Atharv-Shukla-987/Talking-Mirror/talking_mirror/talking_mirror.kicad_pcb

## KiCad design hardware/control_board/control_board.kicad_pcb

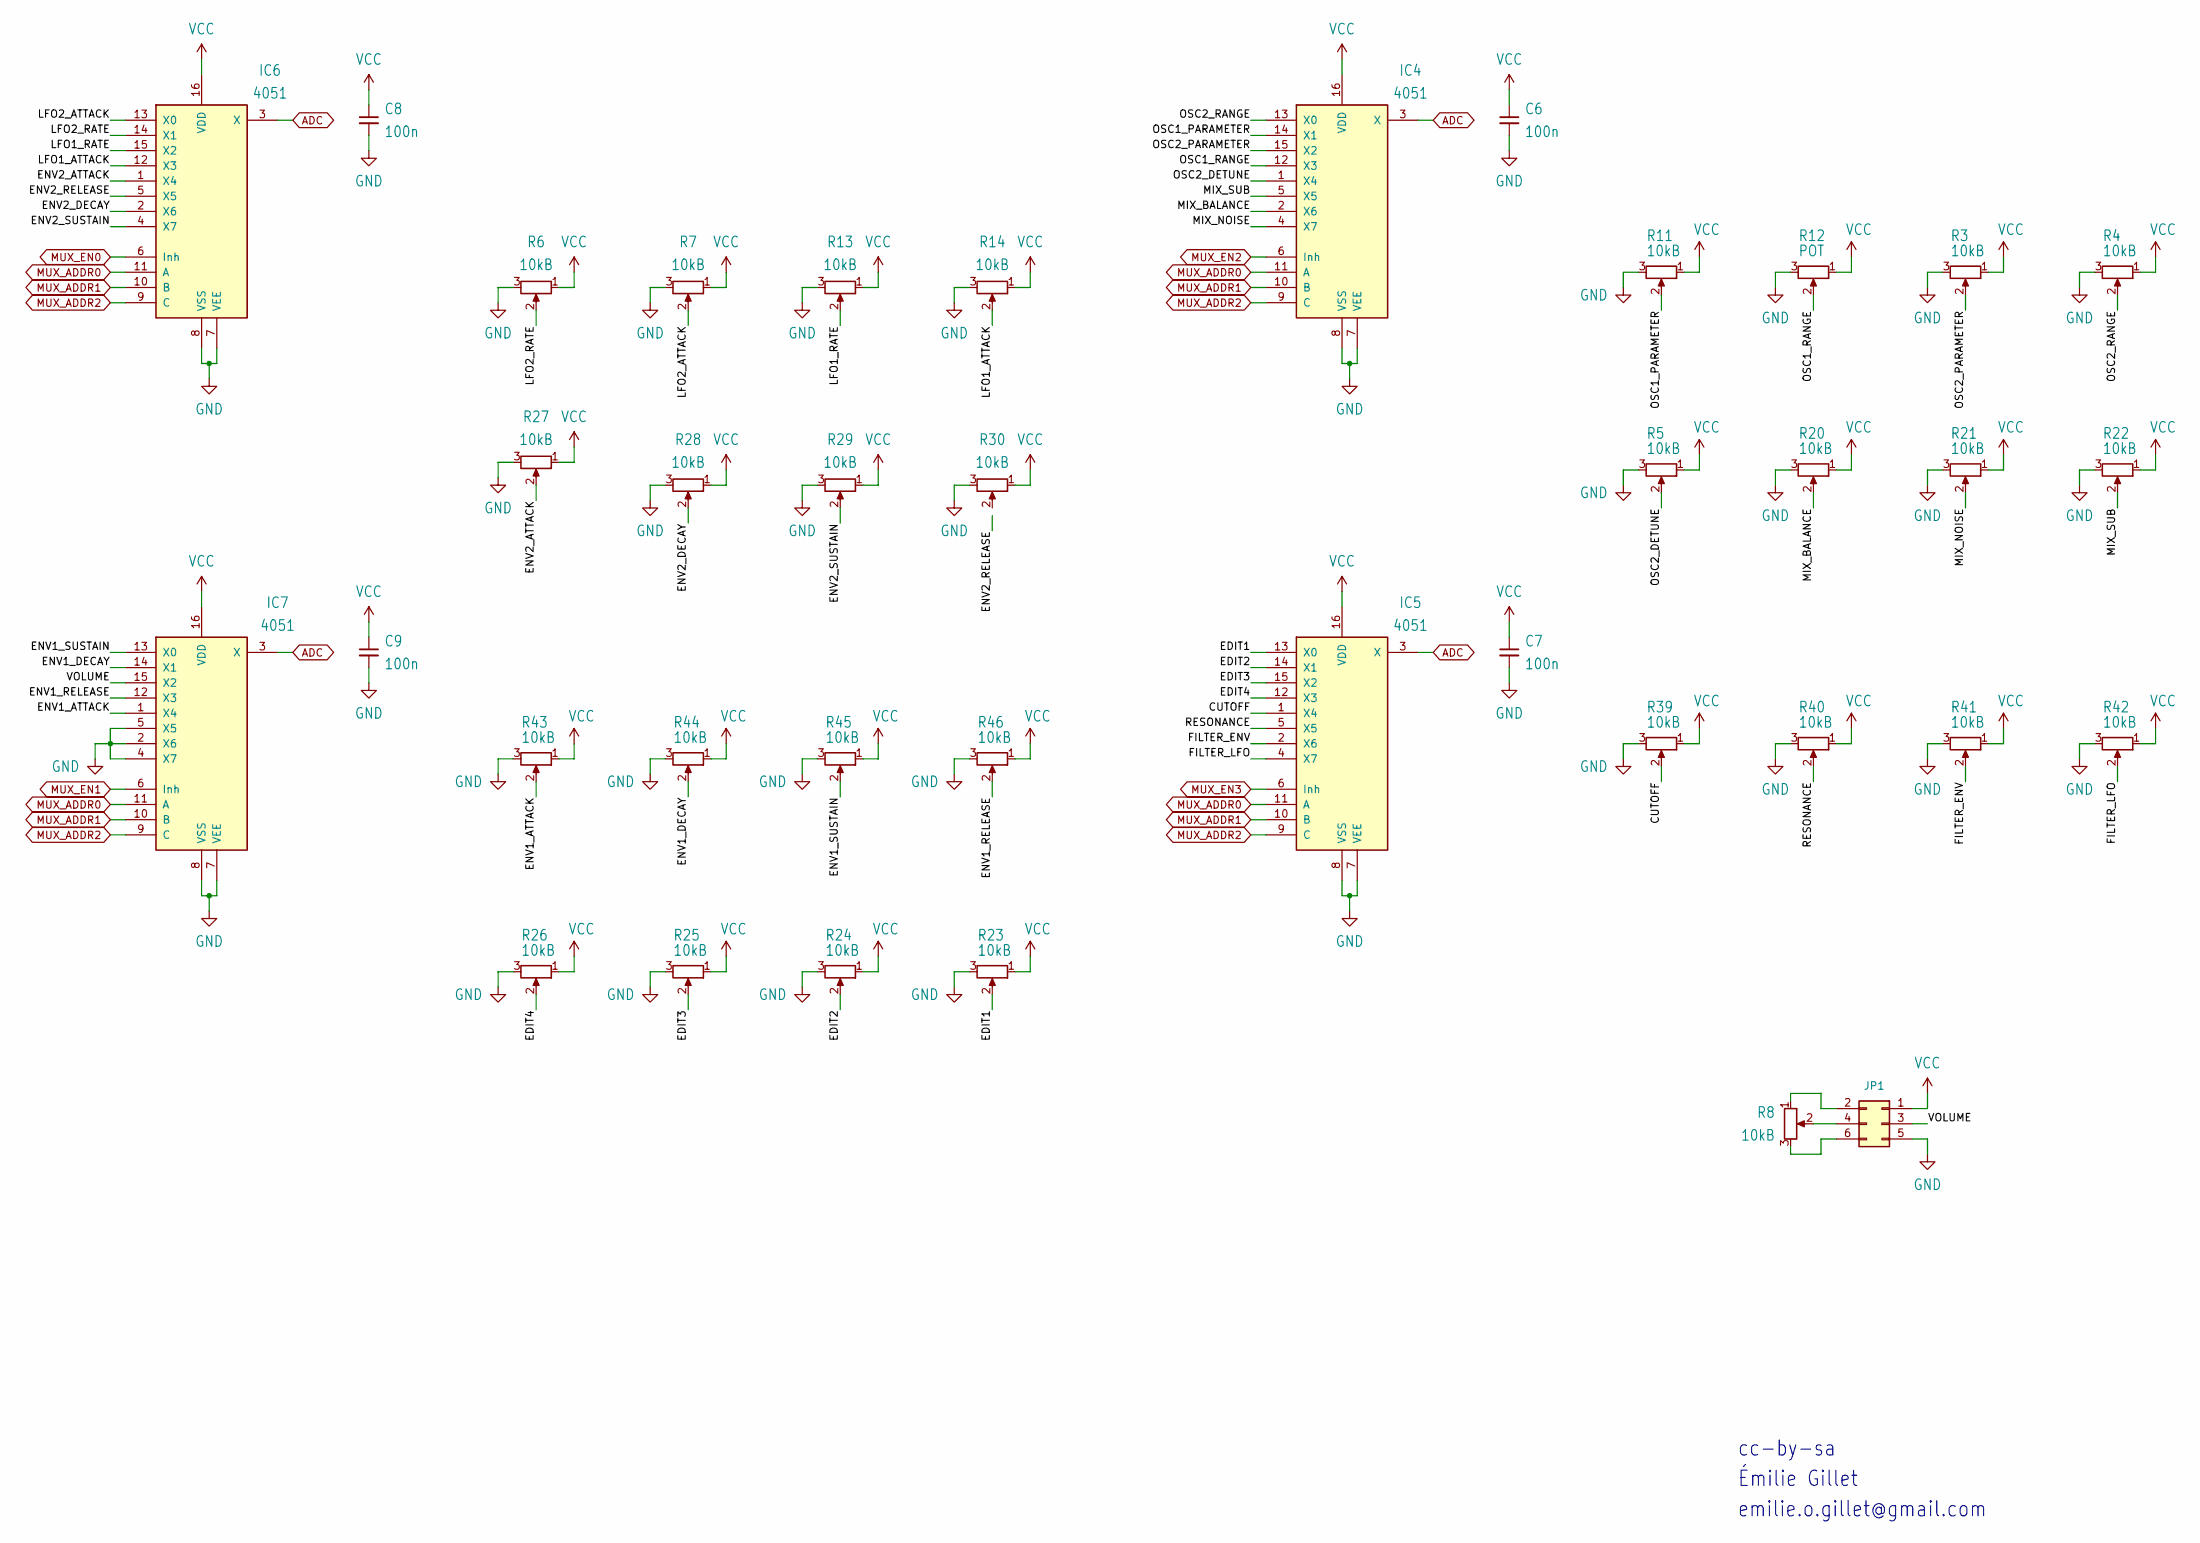
[picture p6: schematic pots.kicad_sch]

Parts:
C6, C7, C8, C9: 100n; C025-024X044
IC4, IC5, IC6, IC7: 4051; DIP-16_W7.62mm_Socket_LongPads
JP1: Conn_02x03_Odd_Even; PinHeader_2x03_P2.54mm_Vertical
R3, R4, R5, R6, R7, R8, R11, R13, R14, R20, R21, R22, R23, R24, R25, R26, R27, R28, R29, R30, R39, R40, R41, R42, R43, R44, R45, R46: 10kB; ALPS_POT_VERTICAL
R12: POT; ALPS_POT_VERTICAL

Connections:
/pots/CUTOFF: IC5.1 (X4), R39.2
/pots/EDIT1: IC5.13 (X0), R23.2
/pots/EDIT2: IC5.14 (X1), R24.2
/pots/EDIT3: IC5.15 (X2), R25.2
/pots/EDIT4: IC5.12 (X3), R26.2
/pots/ENV1_ATTACK: IC7.1 (X4), R43.2
/pots/ENV1_DECAY: IC7.14 (X1), R44.2
/pots/ENV1_RELEASE: IC7.12 (X3), R46.2
/pots/ENV1_SUSTAIN: IC7.13 (X0), R45.2
/pots/ENV2_ATTACK: IC6.1 (X4), R27.2
/pots/ENV2_DECAY: IC6.2 (X6), R28.2
/pots/ENV2_RELEASE: IC6.5 (X5)
/pots/ENV2_SUSTAIN: IC6.4 (X7), R29.2
/pots/FILTER_ENV: IC5.2 (X6), R41.2
/pots/FILTER_LFO: IC5.4 (X7), R42.2
/pots/LFO1_ATTACK: IC6.12 (X3), R14.2
/pots/LFO1_RATE: IC6.15 (X2), R13.2
/pots/LFO2_ATTACK: IC6.13 (X0), R7.2
/pots/LFO2_RATE: IC6.14 (X1), R6.2
/pots/MIX_BALANCE: IC4.2 (X6), R20.2
/pots/MIX_NOISE: IC4.4 (X7), R21.2
/pots/MIX_SUB: IC4.5 (X5), R22.2
/pots/OSC1_PARAMETER: IC4.14 (X1), R11.2
/pots/OSC1_RANGE: IC4.12 (X3), R12.2
/pots/OSC2_DETUNE: IC4.1 (X4), R5.2
/pots/OSC2_PARAMETER: IC4.15 (X2), R3.2
/pots/OSC2_RANGE: IC4.13 (X0), R4.2
/pots/RESONANCE: IC5.5 (X5), R40.2
/pots/VOLUME: IC7.15 (X2), JP1.3
ADC: IC4.3 (X), IC5.3 (X), IC6.3 (X), IC7.3 (X); also elsewhere on the board
GND: C6.2, C7.2, C8.2, C9.2, IC4.7 (VEE), IC4.8 (VSS), IC5.7 (VEE), IC5.8 (VSS), IC6.7 (VEE), IC6.8 (VSS), IC7.2 (X6), IC7.4 (X7), IC7.5 (X5), IC7.7 (VEE), IC7.8 (VSS), JP1.5, R3.3, R4.3, R5.3, R6.3, R7.3, R11.3, R12.3, R13.3, R14.3, R20.3, R21.3, R22.3, R23.3, R24.3, R25.3, R26.3, R27.3, R28.3, R29.3, R30.3, R39.3, R40.3, R41.3, R42.3, R43.3, R44.3, R45.3, R46.3; also elsewhere on the board
MUX_ADDR0: IC4.11 (A), IC5.11 (A), IC6.11 (A), IC7.11 (A); also elsewhere on the board
MUX_ADDR1: IC4.10 (B), IC5.10 (B), IC6.10 (B), IC7.10 (B); also elsewhere on the board
MUX_ADDR2: IC4.9 (C), IC5.9 (C), IC6.9 (C), IC7.9 (C); also elsewhere on the board
MUX_EN0: IC6.6 (Inh); also elsewhere on the board
MUX_EN1: IC7.6 (Inh); also elsewhere on the board
MUX_EN2: IC4.6 (Inh); also elsewhere on the board
MUX_EN3: IC5.6 (Inh); also elsewhere on the board
unnamed: JP1.2, R8.1
unnamed: JP1.4, R8.2
unnamed: JP1.6, R8.3
VCC: C6.1, C7.1, C8.1, C9.1, IC4.16 (VDD), IC5.16 (VDD), IC6.16 (VDD), IC7.16 (VDD), JP1.1, R3.1, R4.1, R5.1, R6.1, R7.1, R11.1, R12.1, R13.1, R14.1, R20.1, R21.1, R22.1, R23.1, R24.1, R25.1, R26.1, R27.1, R28.1, R29.1, R30.1, R39.1, R40.1, R41.1, R42.1, R43.1, R44.1, R45.1, R46.1; also elsewhere on the board

Notes on the sheet:
emilie.o.gillet@gmail.com
cc-by-sa
Émilie Gillet

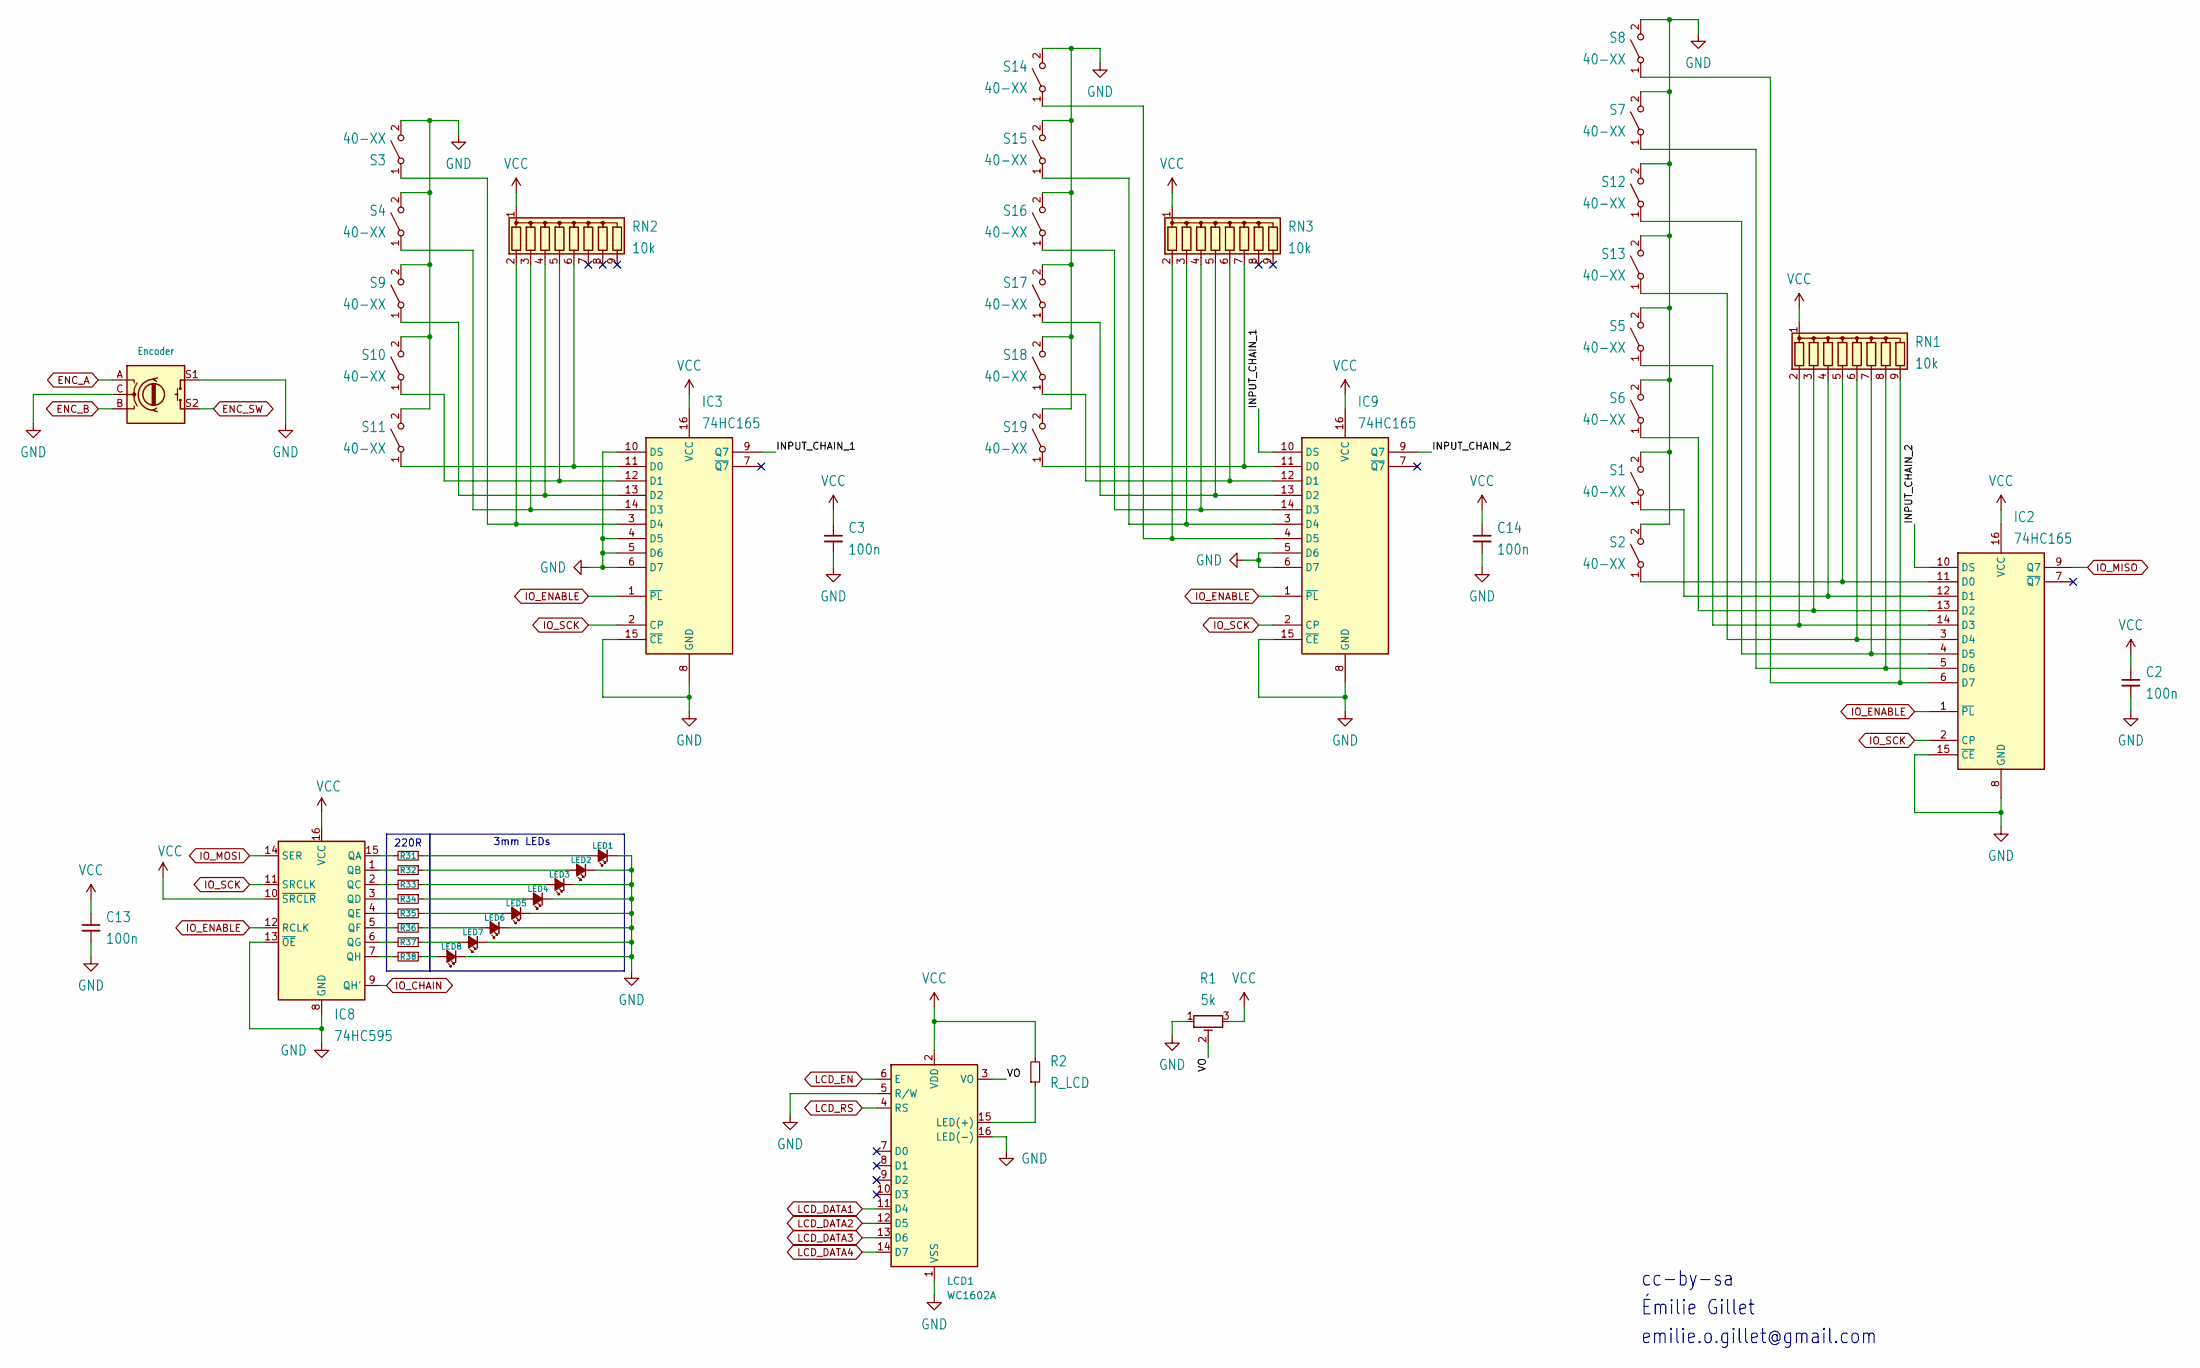
[picture p7: schematic buttons.kicad_sch]

Parts:
C2, C3, C13, C14: 100n; C025-024X044
IC2, IC3, IC9: 74HC165; DIP-16_W7.62mm_Socket_LongPads
IC8: 74HC595; DIP-16_W7.62mm_Socket_LongPads
LCD1: WC1602A
LED1, LED2, LED3, LED4, LED5, LED6, LED7, LED8: LED3MM; LED_D3.0mm
R1: 5k; Potentiometer_Bourns_3296W_Vertical
R2: R_LCD; R_Axial_DIN0204_L3.6mm_D1.6mm_P7.62mm_Horizontal
R31, R32, R33, R34, R35, R36, R37, R38: 220; R_Axial_DIN0204_L3.6mm_D1.6mm_P7.62mm_Horizontal
RN1, RN2, RN3: 10k; R_Array_SIP9
S1, S2, S3, S4, S5, S6, S7, S8, S9, S10, S11, S12, S13, S14, S15, S16, S17, S18, S19: 40-XX; B3F-40XX
SW1: Encoder; ALPS_EC12E_SW

Connections:
/buttons/INPUT_CHAIN_1: IC3.9 (Q7), IC9.10 (DS)
/buttons/INPUT_CHAIN_2: IC2.10 (DS), IC9.9 (Q7)
/buttons/VO: LCD1.3 (VO), R1.2
ENC_A: SW1.A; also elsewhere on the board
ENC_B: SW1.B; also elsewhere on the board
ENC_SW: SW1.S2; also elsewhere on the board
GND: C2.2, C3.2, C13.2, C14.2, IC2.8 (GND), IC2.15 (~CE), IC3.4 (D5), IC3.5 (D6), IC3.6 (D7), IC3.8 (GND), IC3.10 (DS), IC3.15 (~CE), IC8.8 (GND), IC8.13 (~OE), IC9.5 (D6), IC9.6 (D7), IC9.8 (GND), IC9.15 (~CE), LCD1.1 (VSS), LCD1.5 (R/W), LCD1.16 (LED(-)), LED1.1 (K), LED2.1 (K), LED3.1 (K), LED4.1 (K), LED5.1 (K), LED6.1 (K), LED7.1 (K), LED8.1 (K), R1.1, S1.2 (B), S2.2 (B), S3.2 (B), S4.2 (B), S5.2 (B), S6.2 (B), S7.2 (B), S8.2 (B), S9.2 (B), S10.2 (B), S11.2 (B), S12.2 (B), S13.2 (B), S14.2 (B), S15.2 (B), S16.2 (B), S17.2 (B), S18.2 (B), S19.2 (B), SW1.C, SW1.S1; also elsewhere on the board
IO_CHAIN: IC8.9 (QH'); also elsewhere on the board
IO_ENABLE: IC2.1 (~PL), IC3.1 (~PL), IC8.12 (RCLK), IC9.1 (~PL); also elsewhere on the board
IO_MISO: IC2.9 (Q7); also elsewhere on the board
IO_MOSI: IC8.14 (SER); also elsewhere on the board
IO_SCK: IC2.2 (CP), IC3.2 (CP), IC8.11 (SRCLK), IC9.2 (CP); also elsewhere on the board
LCD_DATA1: LCD1.11 (D4); also elsewhere on the board
LCD_DATA2: LCD1.12 (D5); also elsewhere on the board
LCD_DATA3: LCD1.13 (D6); also elsewhere on the board
LCD_DATA4: LCD1.14 (D7); also elsewhere on the board
LCD_EN: LCD1.6 (E); also elsewhere on the board
LCD_RS: LCD1.4 (RS); also elsewhere on the board
unnamed: IC2.11 (D0), RN1.5 (R4), S2.1 (A)
unnamed: IC2.12 (D1), RN1.4 (R3), S1.1 (A)
unnamed: IC2.13 (D2), RN1.3 (R2), S6.1 (A)
unnamed: IC2.14 (D3), RN1.2 (R1), S5.1 (A)
unnamed: IC2.3 (D4), RN1.6 (R5), S13.1 (A)
unnamed: IC2.4 (D5), RN1.7 (R6), S12.1 (A)
unnamed: IC2.5 (D6), RN1.8 (R7), S7.1 (A)
unnamed: IC2.6 (D7), RN1.9 (R8), S8.1 (A)
unnamed: IC3.11 (D0), RN2.6 (R5), S11.1 (A)
unnamed: IC3.12 (D1), RN2.5 (R4), S10.1 (A)
unnamed: IC3.13 (D2), RN2.4 (R3), S9.1 (A)
unnamed: IC3.14 (D3), RN2.3 (R2), S4.1 (A)
unnamed: IC3.3 (D4), RN2.2 (R1), S3.1 (A)
unnamed: IC8.15 (QA), R31.2
unnamed: IC8.1 (QB), R32.2
unnamed: IC8.2 (QC), R33.2
unnamed: IC8.3 (QD), R34.2
unnamed: IC8.4 (QE), R35.2
unnamed: IC8.5 (QF), R36.2
unnamed: IC8.6 (QG), R37.2
unnamed: IC8.7 (QH), R38.2
unnamed: IC9.11 (D0), RN3.7 (R6), S19.1 (A)
unnamed: IC9.12 (D1), RN3.6 (R5), S18.1 (A)
unnamed: IC9.13 (D2), RN3.5 (R4), S17.1 (A)
unnamed: IC9.14 (D3), RN3.4 (R3), S16.1 (A)
unnamed: IC9.3 (D4), RN3.3 (R2), S15.1 (A)
unnamed: IC9.4 (D5), RN3.2 (R1), S14.1 (A)
unnamed: LCD1.15 (LED(+)), R2.1
unnamed: LED1.2 (A), R31.1
unnamed: LED2.2 (A), R32.1
unnamed: LED3.2 (A), R33.1
unnamed: LED4.2 (A), R34.1
unnamed: LED5.2 (A), R35.1
unnamed: LED6.2 (A), R36.1
unnamed: LED7.2 (A), R37.1
unnamed: LED8.2 (A), R38.1
VCC: C2.1, C3.1, C13.1, C14.1, IC2.16 (VCC), IC3.16 (VCC), IC8.10 (~SRCLR), IC8.16 (VCC), IC9.16 (VCC), LCD1.2 (VDD), R1.3, R2.2, RN1.1 (common), RN2.1 (common), RN3.1 (common); also elsewhere on the board

Notes on the sheet:
220R
3mm LEDs
emilie.o.gillet@gmail.com
Émilie Gillet
cc-by-sa

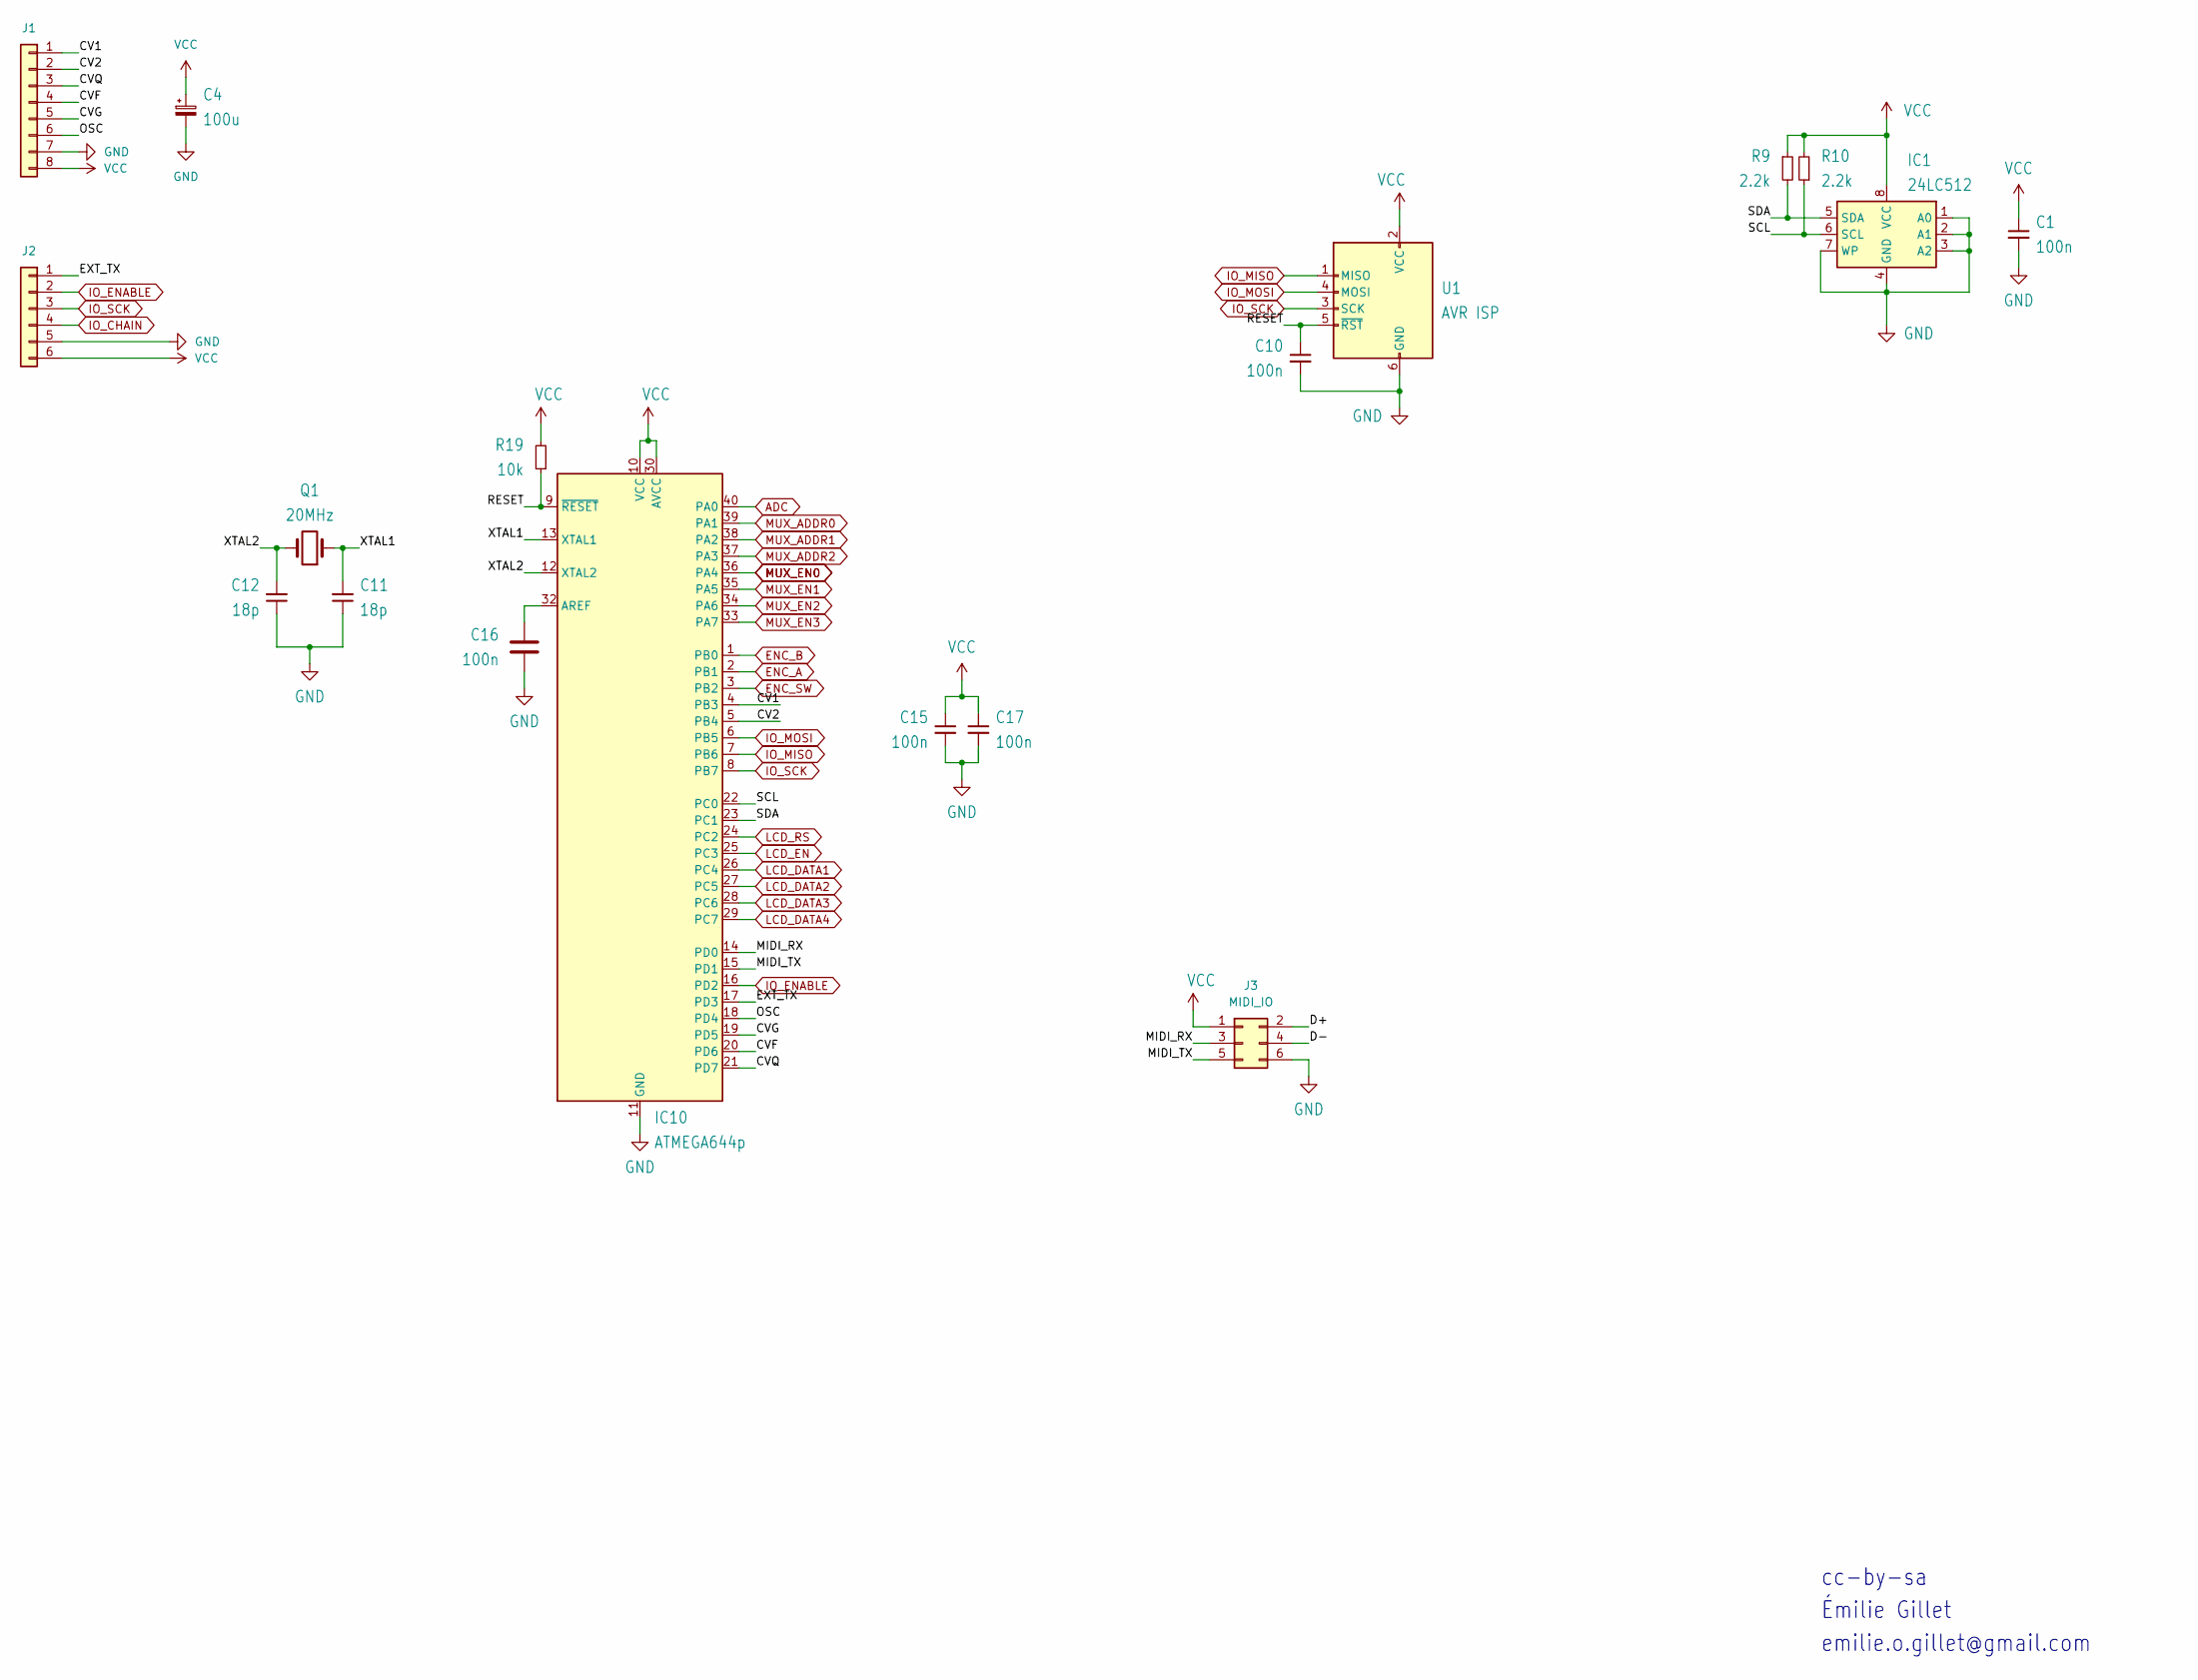
[picture p8: schematic mcu.kicad_sch]

Parts:
C1, C10, C15, C16, C17: 100n; C025-024X044
C4: 100u; CP_Radial_D6.3mm_P2.50mm
C11, C12: 18p; C025-024X044
IC1: 24LC512; DIP-8_W7.62mm_Socket_LongPads
IC10: ATMEGA644p; DIP-40_W15.24mm_Socket_LongPads
J1: Conn_01x08; PinHeader_1x08_P2.54mm_Vertical
J2: Conn_01x06; PinHeader_1x06_P2.54mm_Vertical
J3: MIDI_IO; PinHeader_2x03_P2.54mm_Vertical
Q1: 20MHz; HC49U-V
R9, R10: 2.2k; R_Axial_DIN0204_L3.6mm_D1.6mm_P7.62mm_Horizontal
R19: 10k; 0204_7
U1: AVR ISP; PinHeader_2x03_P2.54mm_Vertical

Connections:
/mcu/CV1: IC10.4 (PB3), J1.1
/mcu/CV2: IC10.5 (PB4), J1.2
/mcu/CVF: IC10.20 (PD6), J1.4
/mcu/CVG: IC10.19 (PD5), J1.5
/mcu/CVQ: IC10.21 (PD7), J1.3
/mcu/D+: J3.2
/mcu/D-: J3.4
/mcu/EXT_TX: IC10.17 (PD3), J2.1
/mcu/MIDI_RX: IC10.14 (PD0), J3.3
/mcu/MIDI_TX: IC10.15 (PD1), J3.5
/mcu/OSC: IC10.18 (PD4), J1.6
/mcu/RESET: C10.1, IC10.9 (~RESET), R19.1, U1.5 (~RST)
/mcu/SCL: IC1.6 (SCL), IC10.22 (PC0), R10.1
/mcu/SDA: IC1.5 (SDA), IC10.23 (PC1), R9.2
/mcu/XTAL1: C11.2, IC10.13 (XTAL1), Q1.1
/mcu/XTAL2: C12.2, IC10.12 (XTAL2), Q1.2
ADC: IC10.40 (PA0); also elsewhere on the board
ENC_A: IC10.2 (PB1); also elsewhere on the board
ENC_B: IC10.1 (PB0); also elsewhere on the board
ENC_SW: IC10.3 (PB2); also elsewhere on the board
GND: C1.2, C4.2, C10.2, C11.1, C12.1, C15.2, C16.2, C17.2, IC1.1 (A0), IC1.2 (A1), IC1.3 (A2), IC1.4 (GND), IC1.7 (WP), IC10.11 (GND), IC10.31 (GND), J1.7, J2.5, J3.6, U1.6 (GND); also elsewhere on the board
IO_CHAIN: J2.4; also elsewhere on the board
IO_ENABLE: IC10.16 (PD2), J2.2; also elsewhere on the board
IO_MISO: IC10.7 (PB6), U1.1 (MISO); also elsewhere on the board
IO_MOSI: IC10.6 (PB5), U1.4 (MOSI); also elsewhere on the board
IO_SCK: IC10.8 (PB7), J2.3, U1.3 (SCK); also elsewhere on the board
LCD_DATA1: IC10.26 (PC4); also elsewhere on the board
LCD_DATA2: IC10.27 (PC5); also elsewhere on the board
LCD_DATA3: IC10.28 (PC6); also elsewhere on the board
LCD_DATA4: IC10.29 (PC7); also elsewhere on the board
LCD_EN: IC10.25 (PC3); also elsewhere on the board
LCD_RS: IC10.24 (PC2); also elsewhere on the board
MUX_ADDR0: IC10.39 (PA1); also elsewhere on the board
MUX_ADDR1: IC10.38 (PA2); also elsewhere on the board
MUX_ADDR2: IC10.37 (PA3); also elsewhere on the board
MUX_EN0: IC10.36 (PA4); also elsewhere on the board
MUX_EN1: IC10.35 (PA5); also elsewhere on the board
MUX_EN2: IC10.34 (PA6); also elsewhere on the board
MUX_EN3: IC10.33 (PA7); also elsewhere on the board
unnamed: C16.1, IC10.32 (AREF)
VCC: C1.1, C4.1, C15.1, C17.1, IC1.8 (VCC), IC10.10 (VCC), IC10.30 (AVCC), J1.8, J2.6, J3.1, R9.1, R10.2, R19.2, U1.2 (VCC); also elsewhere on the board

Notes on the sheet:
cc-by-sa
Émilie Gillet
emilie.o.gillet@gmail.com

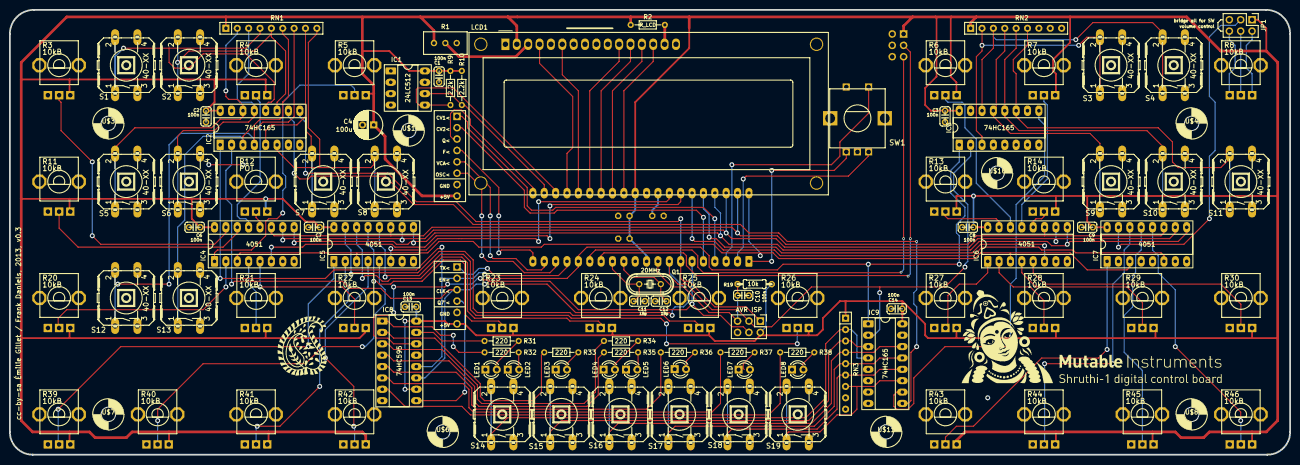
[picture p9: board control_board.kicad_pcb from above]

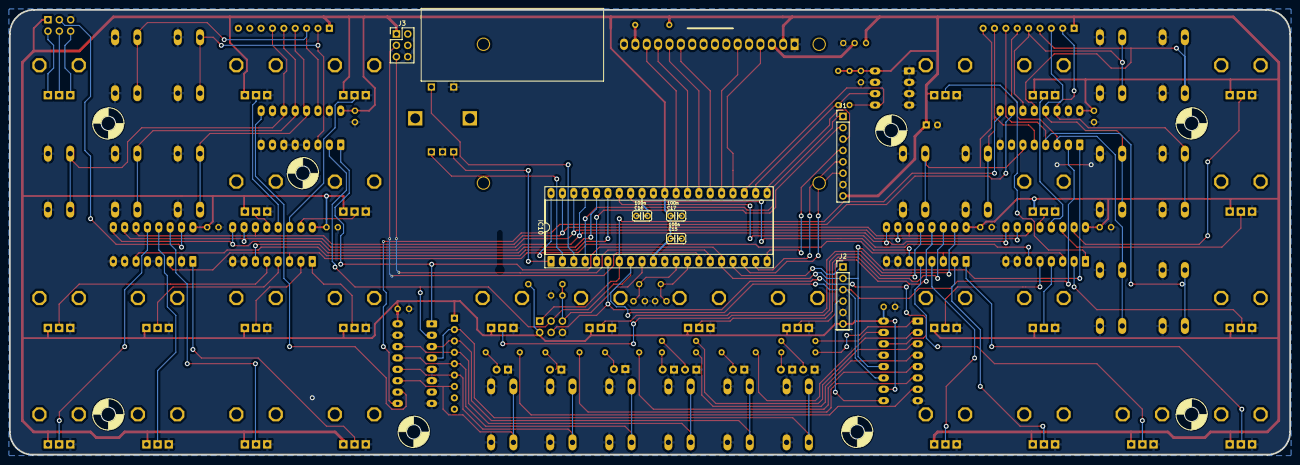
[picture p10: board control_board.kicad_pcb from below]

Board: 2 copper layers, 286.0 x 99.4 mm, 116 parts (7 on the bottom side), 109 nets.

Other parts of the board:
U$1, U$3, U$4, U$6, U$7, U$8, U$10, U$11: MountingHole_M3
U$5: V2_LOGO_SHRUTHI_DIGITAL
U$9: V2_LOGO_DINGBAT1
